LUOaini1213/bridge-bim/model/project_replay/bridge_2027-07-01_1000.png

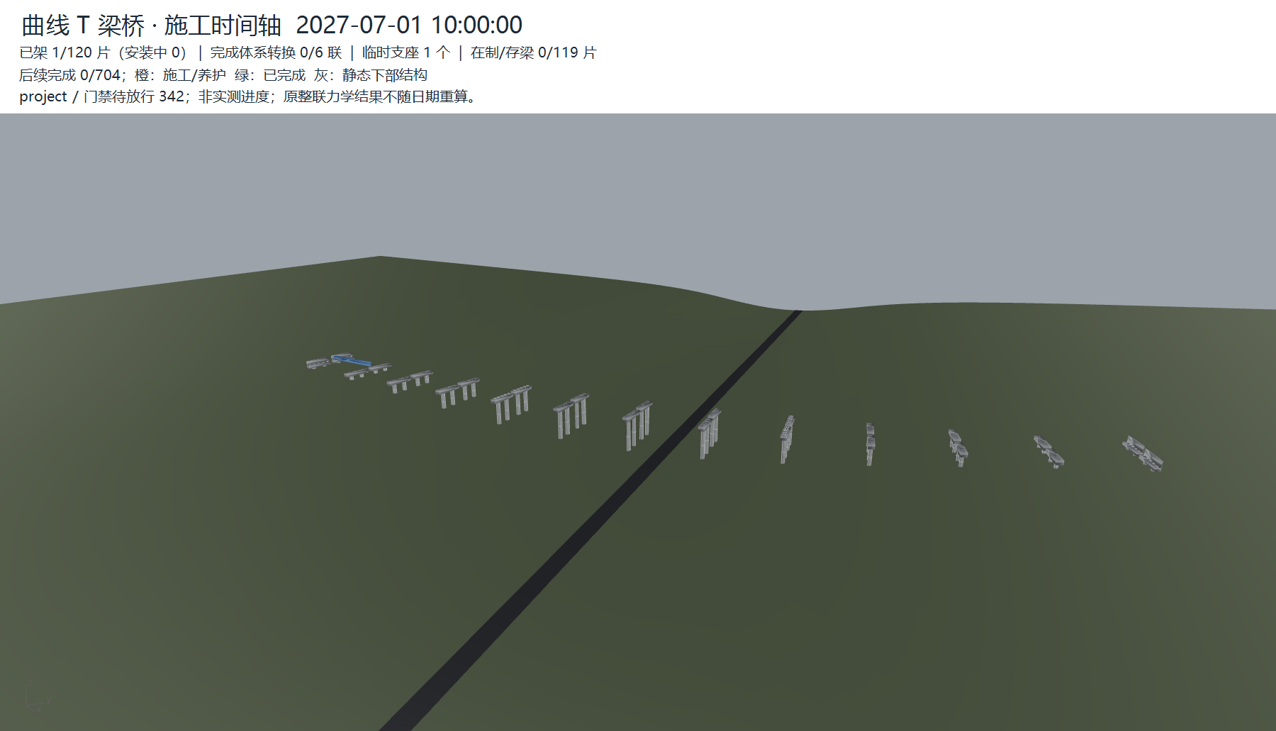
model/project_replay/bridge_2027-07-01_1000.png
