LUOaini1213/bridge-bim/model/replay/bridge_2027-02-20_1600_M1_L-U2-G3.png

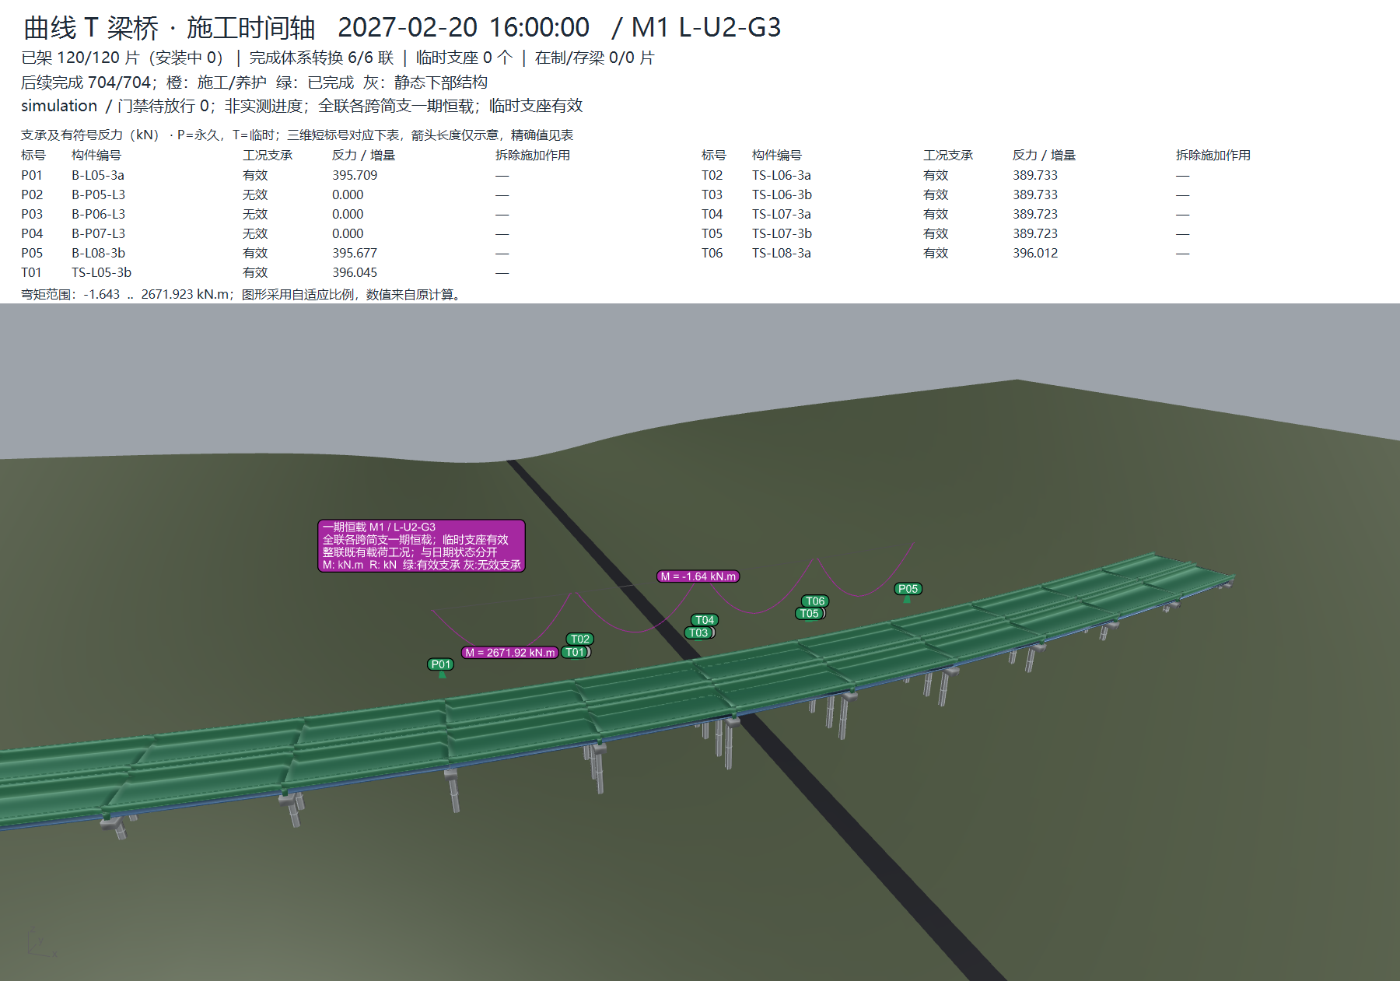
model/replay/bridge_2027-02-20_1600_M1_L-U2-G3.png
